einars/rtu-lab-sensori/kicad/ploterim/ploterim.kicad_sch

## KiCad design kicad/ploterim/ploterim.kicad_sch (2023-12-01, an earlier design)

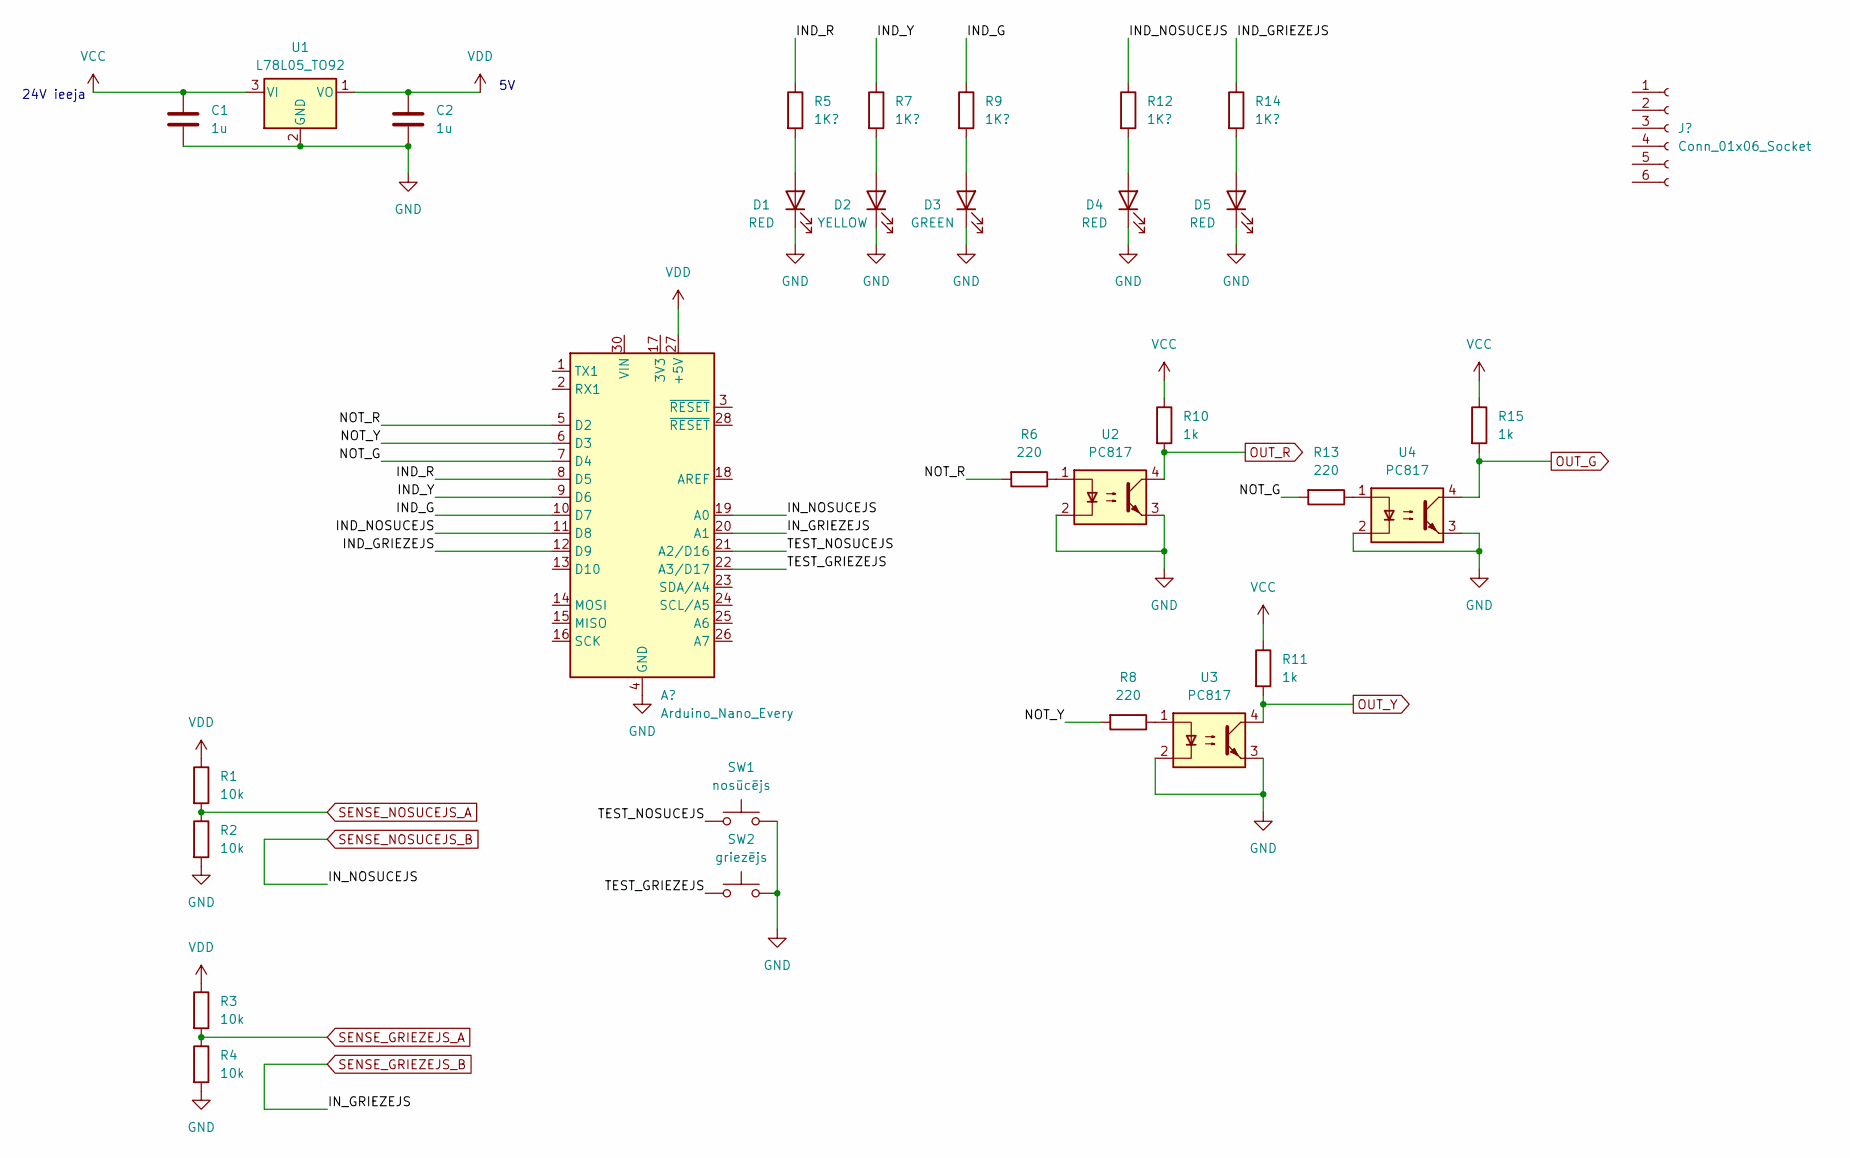
[picture p15: schematic ploterim.kicad_sch]

Parts:
C1, C2: 1u
D1, D4, D5: RED
D2: YELLOW
D3: GREEN
R1, R2, R3, R4: 10k
R5, R7, R9, R12, R14: 1K?
R6, R8, R13: 220
R10, R11, R15: 1k
SW1: nosūcējs
SW2: griezējs
U1: L78L05_TO92; TO-92_Inline
U2, U3, U4: PC817; DIP-4_W7.62mm

Connections:
GND: C1.2, C2.2, D1.1 (K), D2.1 (K), D3.1 (K), D4.1 (K), D5.1 (K), R2.2, R4.2, SW1.2, SW2.2, U1.2 (GND), U2.2, U2.3, U3.2, U3.3, U4.2, U4.3
IND_G: R9.1
IND_GRIEZEJS: R14.1
IND_NOSUCEJS: R12.1
IND_R: R5.1
IND_Y: R7.1
NOT_G: R13.2
NOT_R: R6.2
NOT_Y: R8.2
unnamed: D1.2 (A), R5.2
unnamed: D2.2 (A), R7.2
unnamed: D3.2 (A), R9.2
unnamed: D4.2 (A), R12.2
unnamed: D5.2 (A), R14.2
unnamed: R6.1, U2.1
unnamed: R8.1, U3.1
unnamed: R13.1, U4.1
OUT_G: R15.2, U4.4
OUT_R: R10.2, U2.4
OUT_Y: R11.2, U3.4
SENSE_GRIEZEJS_A: R3.2, R4.1
SENSE_NOSUCEJS_A: R1.2, R2.1
TEST_GRIEZEJS: SW2.1
TEST_NOSUCEJS: SW1.1
VCC: C1.1, R10.1, R11.1, R15.1, U1.3 (VI)
VDD: C2.1, R1.1, R3.1, U1.1 (VO)

Notes on the sheet:
24V ieeja
